air-command/horizon/03_Booster/A1_Pressure_Chamber/A2_Bottom_EndCap/P7_CF_Sleeve/info.txt

290mm long 2.5" Medium Carbon fiber sleeve
