air-command/horizon/03_Booster/A1_Pressure_Chamber/A2_Bottom_EndCap/P8_FG_Nozzle_Tow/info.txt

Nozzle is prepped by sanding and washing in Acetone. 
The nozzle is placed by itself on the nozzle mold, and 7 x 1m FG tow (made from 200gsm cloth) is wrapped around the top of the nozzle. 
This is then sanded smooth on the outside.
