air-command/horizon/03_Booster/A1_Pressure_Chamber/A3_Inner_Tube/P1_Mandrel/info.txt

80mm Diameter PVC mandrel 2m long.
Sanded smooth with 400grit and 1200grit sandpaper.
Waxed 3x with Carnauba Wax mold release.
