air-command/horizon/03_Booster/A1_Pressure_Chamber/A4_Nozzle_Oversleeve/P1_Nozzle/info.txt

The nozzle is made from a 42mm aluminium bar cut to a length of 51mm before being machined.
