air-command/horizon/03_Booster/A1_Pressure_Chamber/A4_Nozzle_Oversleeve/P2_Oring/info.txt

The oring is inserted into the nozzle sleeve to help seal.
It is a 024 o-ring.
