air-command/horizon/01_Launcher/A1_Air_Control_Box/Control_Box_Seals.JPG

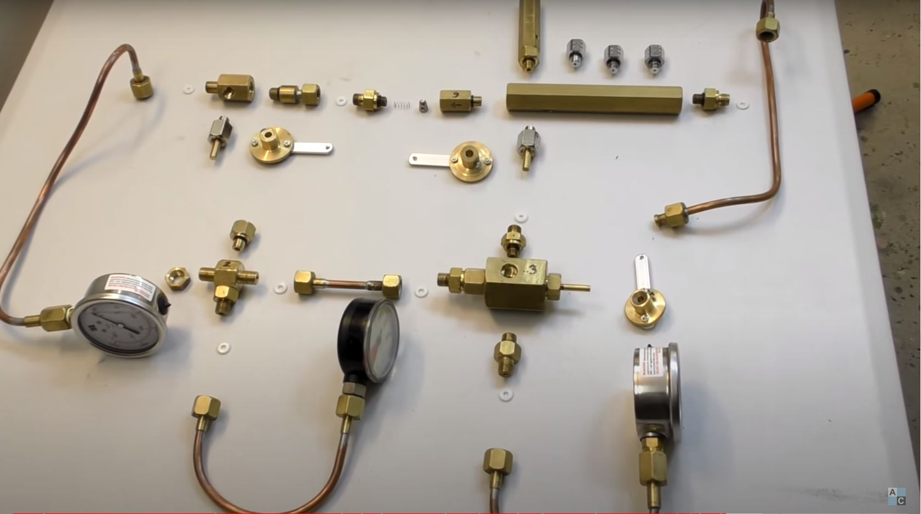
01_Launcher/A1_Air_Control_Box/Control_Box_Seals.JPG
