air-command/horizon/01_Launcher/A1_Air_Control_Box/Seals.jpg

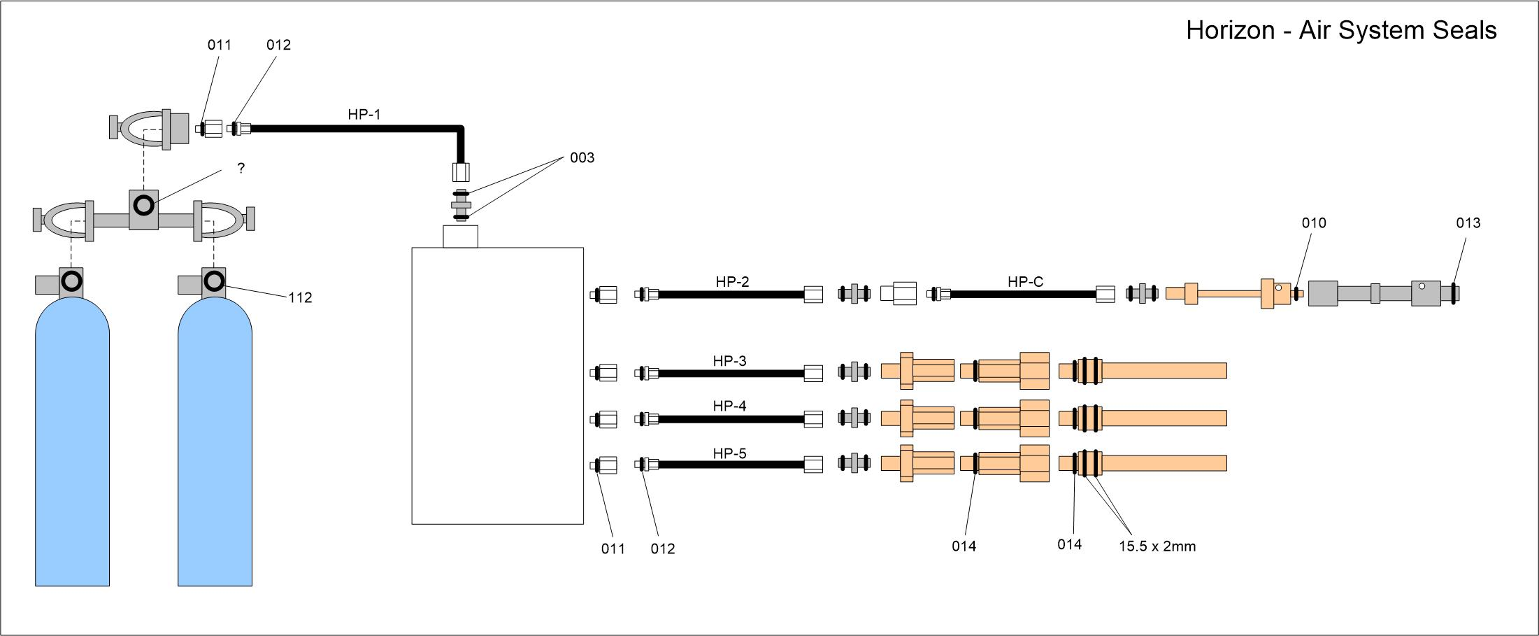
01_Launcher/A1_Air_Control_Box/Seals.jpg
