air-command/horizon/03_Booster/A2_Deployment/A2_Main_Deploy/photos/CameraPod2.jpg

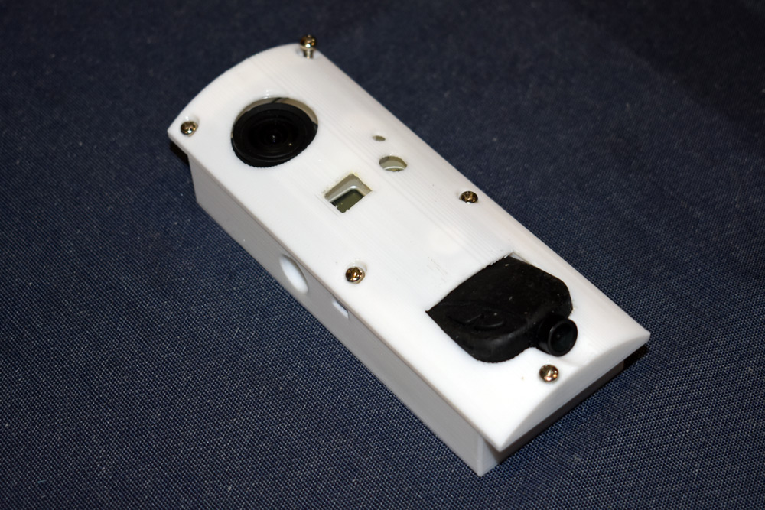
03_Booster/A2_Deployment/A2_Main_Deploy/photos/CameraPod2.jpg
