air-command/horizon/03_Booster/A2_Deployment/A2_Main_Deploy/photos/CameraPod3.jpg

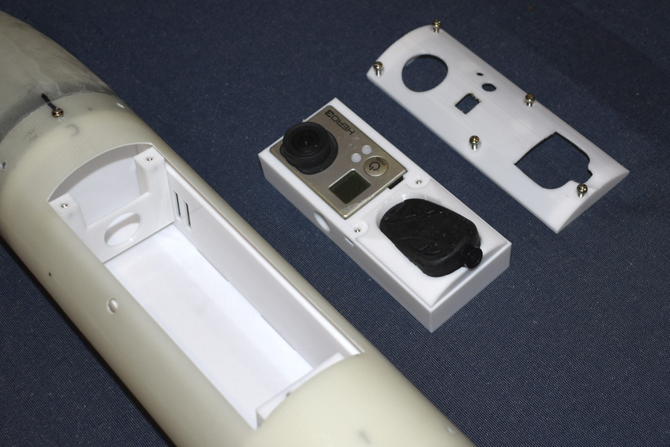
03_Booster/A2_Deployment/A2_Main_Deploy/photos/CameraPod3.jpg
