air-command/horizon/03_Booster/A3_Lower_Bracket/A3_Lower_Bracket.JPG

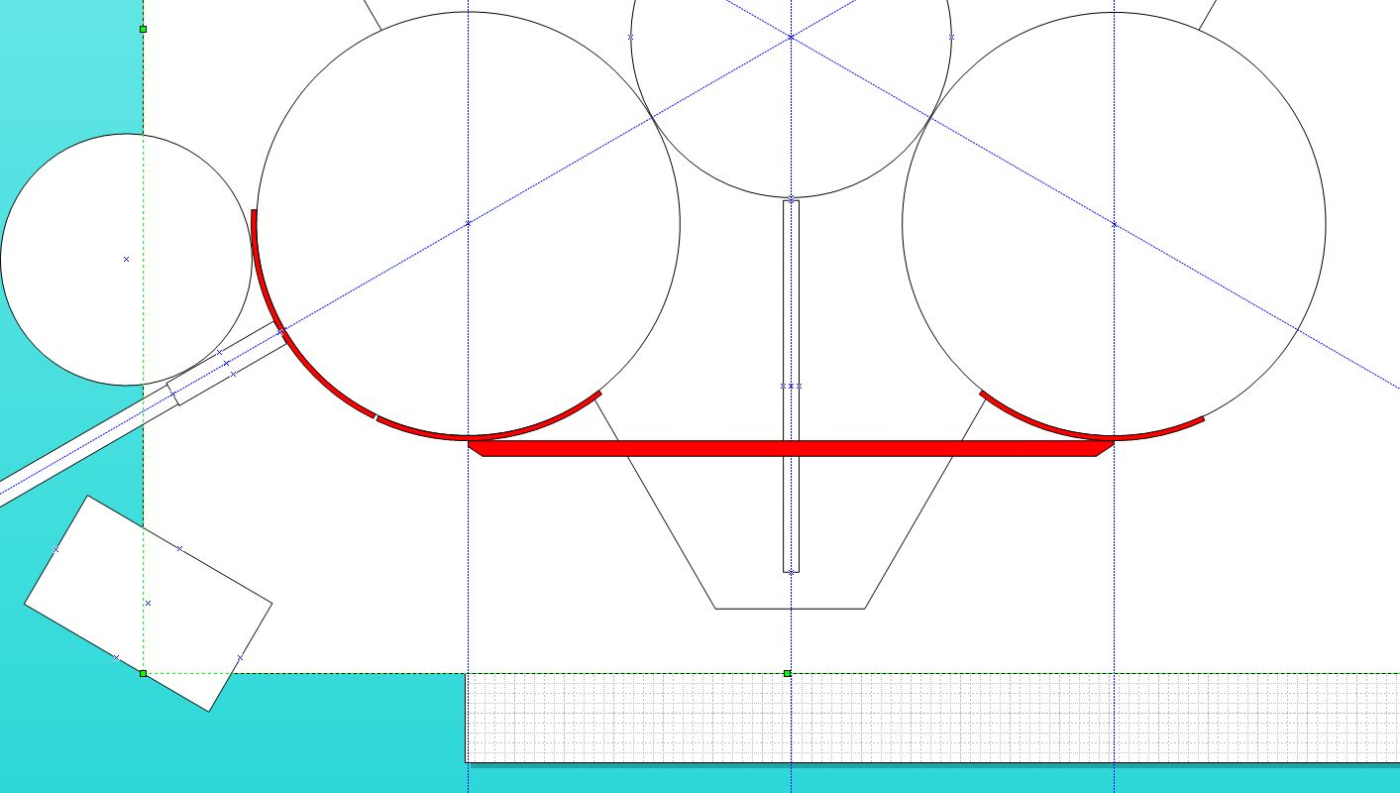
03_Booster/A3_Lower_Bracket/A3_Lower_Bracket.JPG
