air-command/horizon/03_Booster/A8_Top_Ring/ring1.jpg

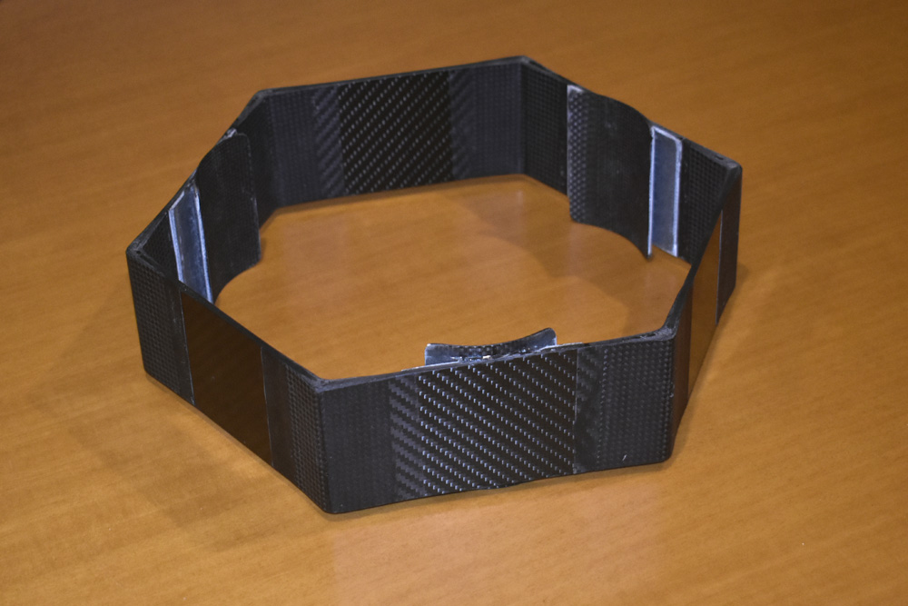
03_Booster/A8_Top_Ring/ring1.jpg
