air-command/horizon/03_Booster/A8_Top_Ring/ring2.jpg

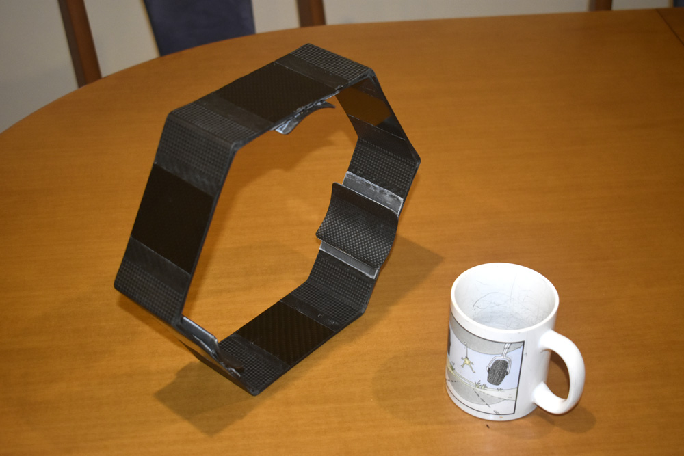
03_Booster/A8_Top_Ring/ring2.jpg
