air-command/horizon/03_Booster/A8_Top_Ring/ring3.jpg

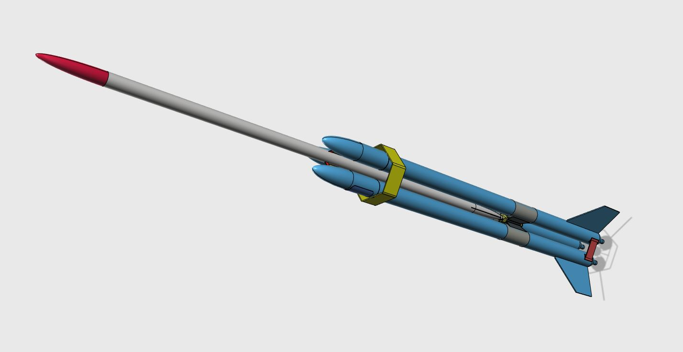
03_Booster/A8_Top_Ring/ring3.jpg
