air-command/horizon/Flight_Data/Booster/pod_a_horizon_2.JPG

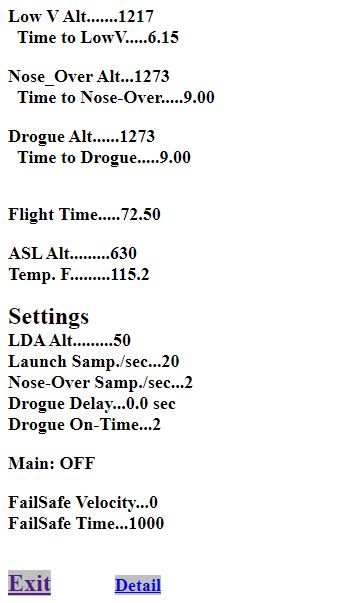
Flight_Data/Booster/pod_a_horizon_2.JPG
