air-command/horizon/Flight_Data/Booster/pod_b_horizon_1.JPG

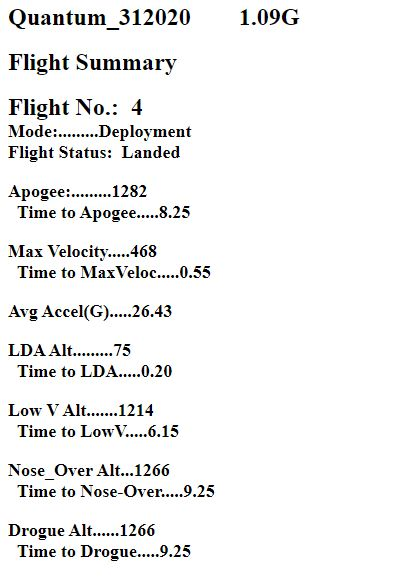
Flight_Data/Booster/pod_b_horizon_1.JPG
