air-command/horizon/Flight_Data/Sustainer/horizon.JPG

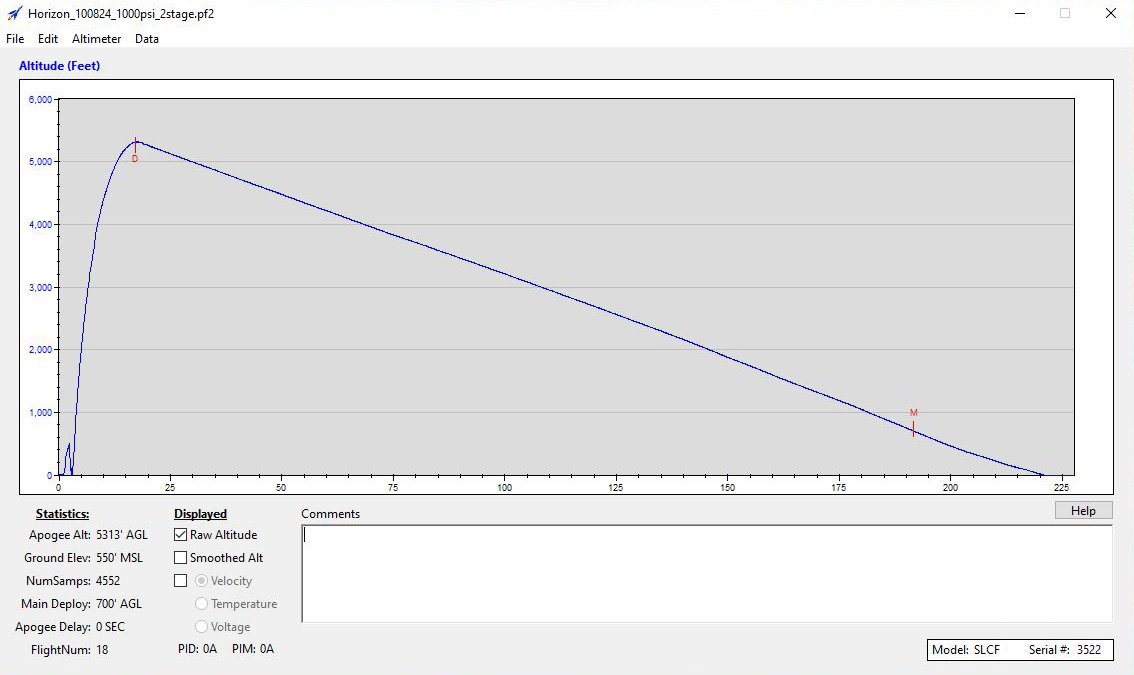
Flight_Data/Sustainer/horizon.JPG
