air-command/horizon/03_Booster/A2_Deployment/A2_Main_Deploy/P3_Body/P3_Body.stl

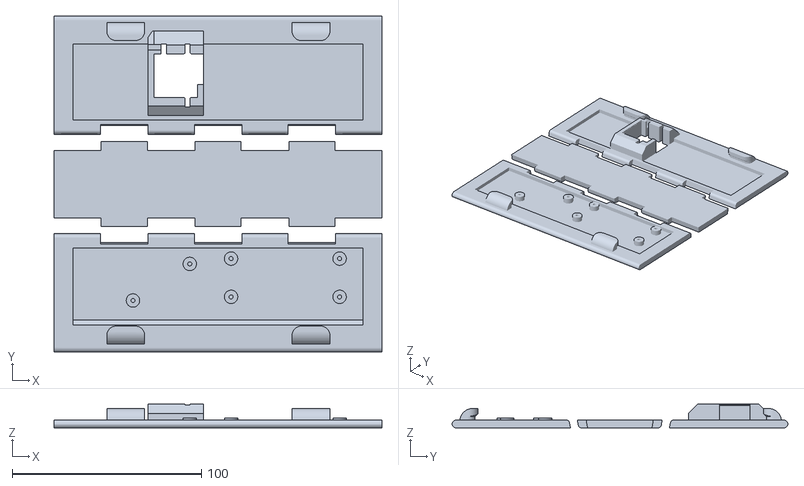
[picture p35: CAD file, 2025-02-12]
03_Booster/A2_Deployment/A2_Main_Deploy/P3_Body/P3_Body.stl
173.0 x 177.4 x 12.7
