air-command/horizon/03_Booster/A2_Deployment/A2_Main_Deploy/P3_Body_Back/P3_Body_Back.stl

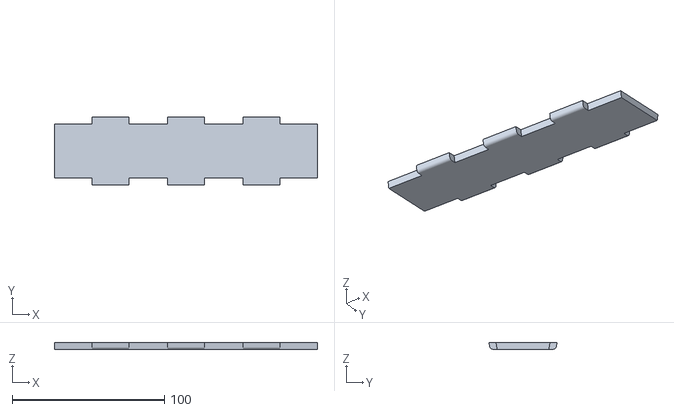
[picture p36: CAD file, 2025-02-12]
03_Booster/A2_Deployment/A2_Main_Deploy/P3_Body_Back/P3_Body_Back.stl
173.0 x 44.8 x 4.30
