air-command/horizon/03_Booster/A2_Deployment/A2_Main_Deploy/P4_Body_Servo/P4_Body_Servo.stl

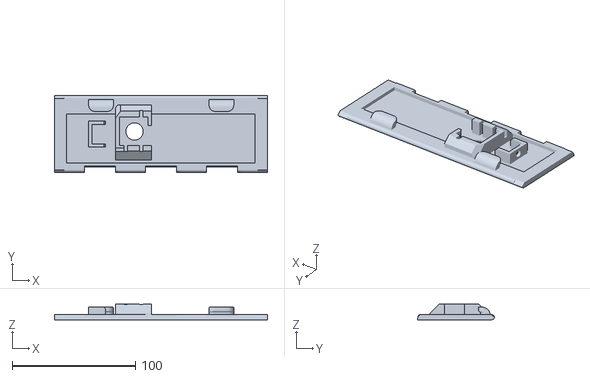
[picture p37: CAD file, 2025-02-12]
03_Booster/A2_Deployment/A2_Main_Deploy/P4_Body_Servo/P4_Body_Servo.stl
173.0 x 62.6 x 12.7
