air-command/horizon/03_Booster/A2_Deployment/A2_Main_Deploy/P5_Body_Quantum/P5_Body_Quantum.stl

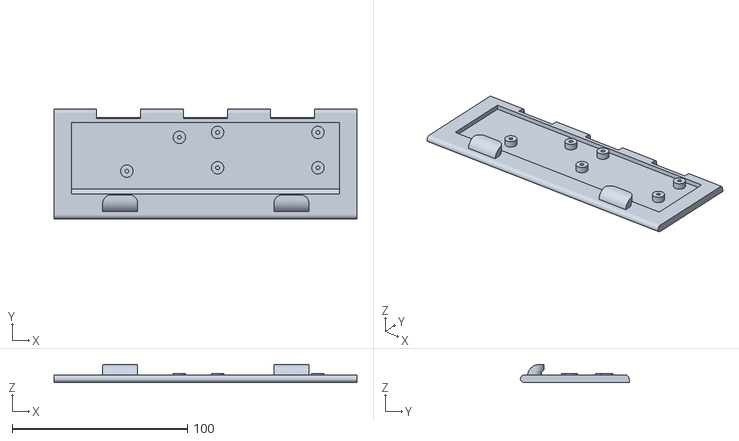
[picture p38: CAD file, 2025-02-12]
03_Booster/A2_Deployment/A2_Main_Deploy/P5_Body_Quantum/P5_Body_Quantum.stl
173.0 x 62.5 x 10.3
