air-command/horizon/03_Booster/A2_Deployment/A2_Main_Deploy/P6_Body_Rokit/P6_Body_Rokit.stl

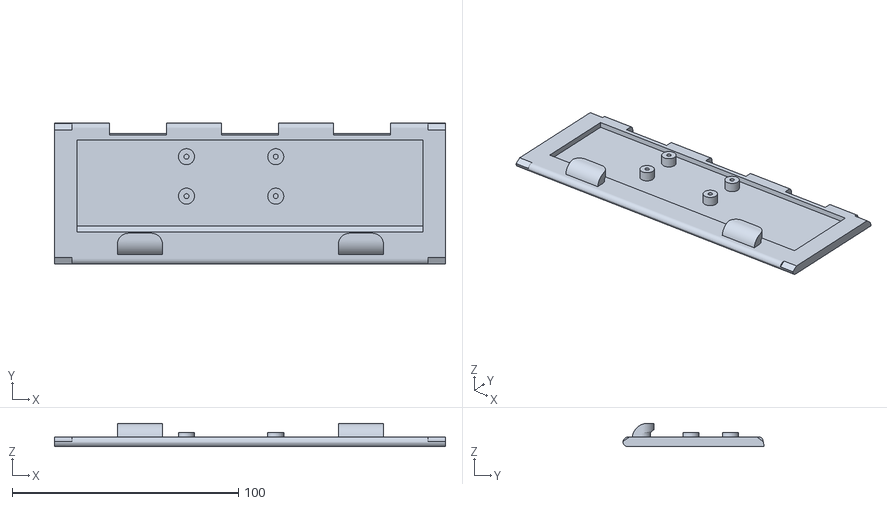
[picture p39: CAD file, 2025-02-12]
03_Booster/A2_Deployment/A2_Main_Deploy/P6_Body_Rokit/P6_Body_Rokit.stl
173.0 x 62.5 x 10.3
