air-command/horizon/03_Booster/A2_Deployment/A2_Main_Deploy/P7_Battery_Holder_A/P7_Battery_Holder_A.stl

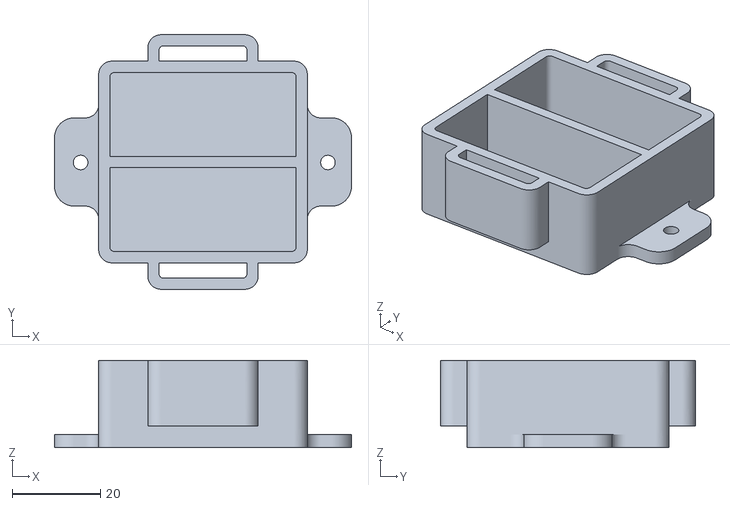
[picture p40: CAD file, 2025-02-12]
03_Booster/A2_Deployment/A2_Main_Deploy/P7_Battery_Holder_A/P7_Battery_Holder_A.stl
67.3 x 57.6 x 19.8
