air-command/horizon/03_Booster/A2_Deployment/A2_Main_Deploy/P8_Battery_Holder_B/P8_Battery_Holder_B.stl

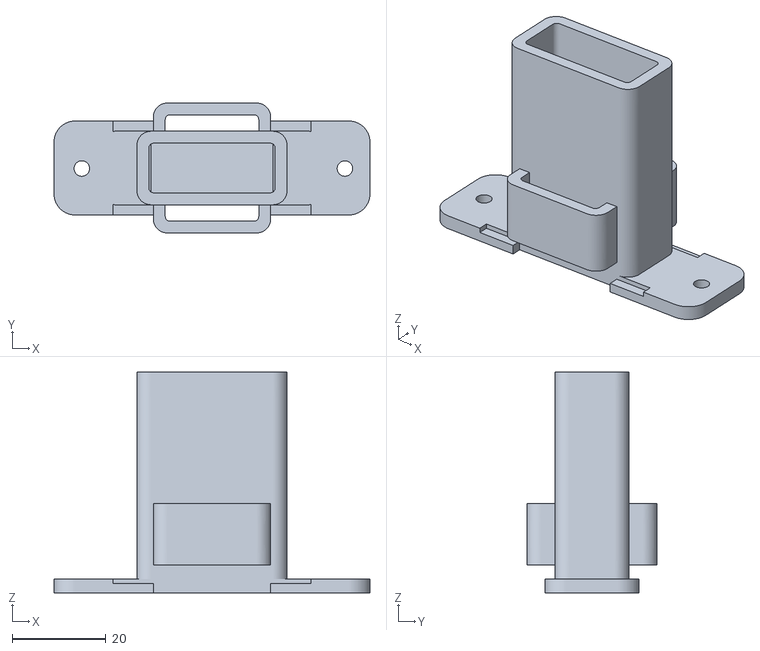
[picture p41: CAD file, 2025-02-12]
03_Booster/A2_Deployment/A2_Main_Deploy/P8_Battery_Holder_B/P8_Battery_Holder_B.stl
67.3 x 27.6 x 47.0
