air-command/horizon/03_Booster/A2_Deployment/A2_Main_Deploy/P9_Ejector_Plate/P9_Ejector_Plate.stl

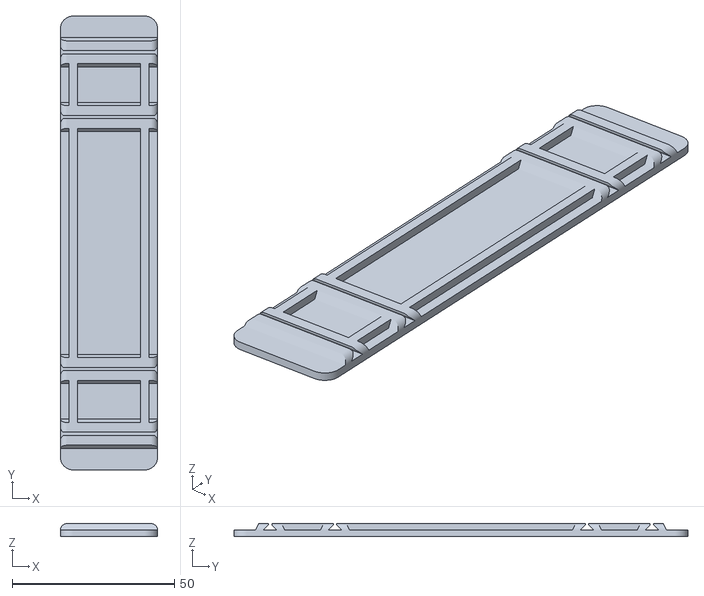
[picture p42: CAD file, 2025-02-12]
03_Booster/A2_Deployment/A2_Main_Deploy/P9_Ejector_Plate/P9_Ejector_Plate.stl
30.0 x 140.0 x 4.00
