air-command/horizon/03_Booster/A2_Deployment/A3_Camera_Pod/A1_Cameras/P4_Camera_Mounts.stl

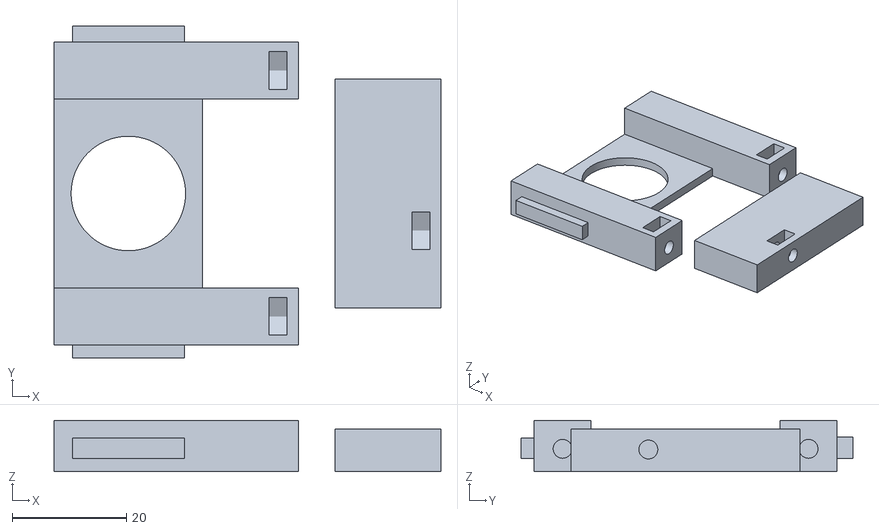
[picture p43: CAD file, 2025-02-12]
03_Booster/A2_Deployment/A3_Camera_Pod/A1_Cameras/P4_Camera_Mounts.stl
67.7 x 58.0 x 9.00
