air-command/horizon/03_Booster/A2_Deployment/A3_Camera_Pod/GOPRO_HERO_3.stp

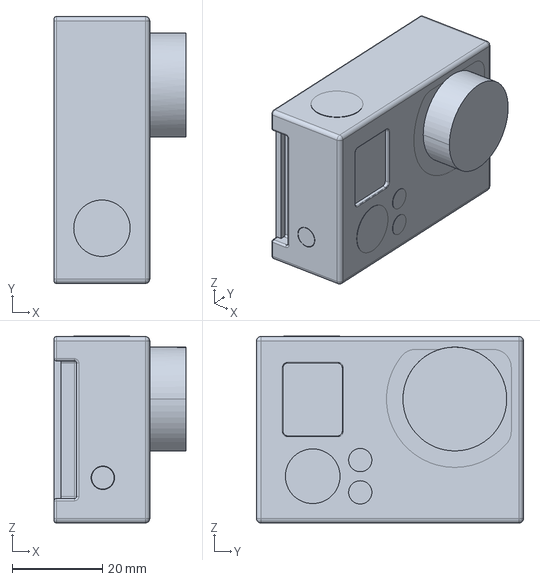
[picture p44: CAD file, 2025-02-12]
03_Booster/A2_Deployment/A3_Camera_Pod/GOPRO_HERO_3.stp
29.2 x 59.1 x 41.4 mm
