air-command/horizon/03_Booster/A2_Deployment/A3_Camera_Pod/P1_Top_Bulkhead/P1_Top_Bulkhead.stl

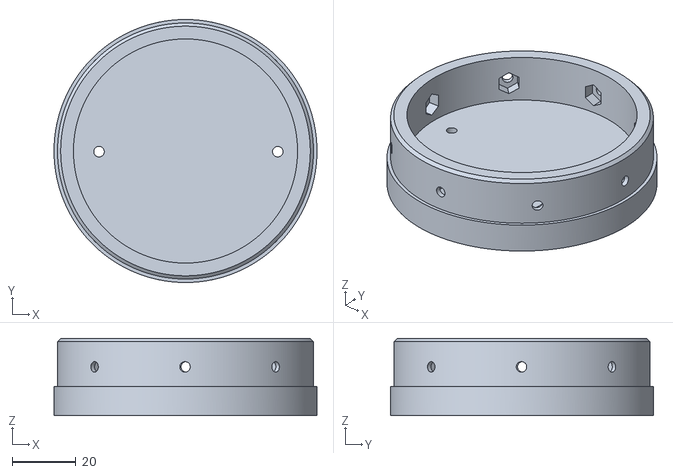
[picture p45: CAD file, 2025-02-12]
03_Booster/A2_Deployment/A3_Camera_Pod/P1_Top_Bulkhead/P1_Top_Bulkhead.stl
82.4 x 82.4 x 24.2
