air-command/horizon/03_Booster/A2_Deployment/A3_Camera_Pod/P2_Bottom_Bulkhead/P2_Bottom_Bulkhead.stl

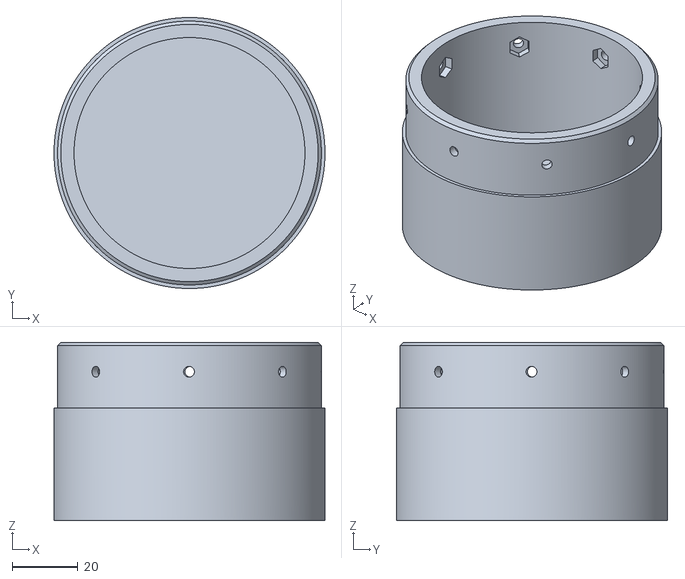
[picture p46: CAD file, 2025-02-12]
03_Booster/A2_Deployment/A3_Camera_Pod/P2_Bottom_Bulkhead/P2_Bottom_Bulkhead.stl
82.4 x 82.4 x 54.2
