air-command/horizon/03_Booster/A2_Deployment/A3_Camera_Pod/P3_Body_Back/P3_Body_Back.stl

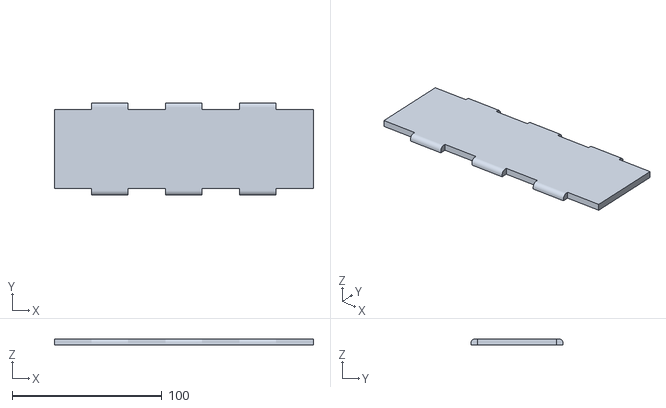
[picture p47: CAD file, 2025-02-12]
03_Booster/A2_Deployment/A3_Camera_Pod/P3_Body_Back/P3_Body_Back.stl
173.0 x 61.5 x 4.30
