air-command/horizon/03_Booster/A2_Deployment/A3_Camera_Pod/P4_Body_Left/P4_Body_Left.stl

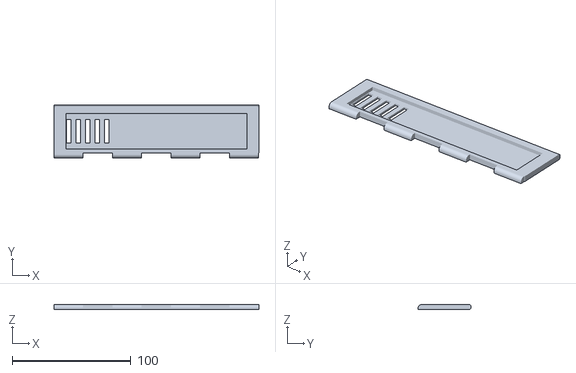
[picture p48: CAD file, 2025-02-12]
03_Booster/A2_Deployment/A3_Camera_Pod/P4_Body_Left/P4_Body_Left.stl
173.0 x 44.5 x 4.30
