air-command/horizon/03_Booster/A2_Deployment/A3_Camera_Pod/P6_Battery_808/P6_Battery_808.stl

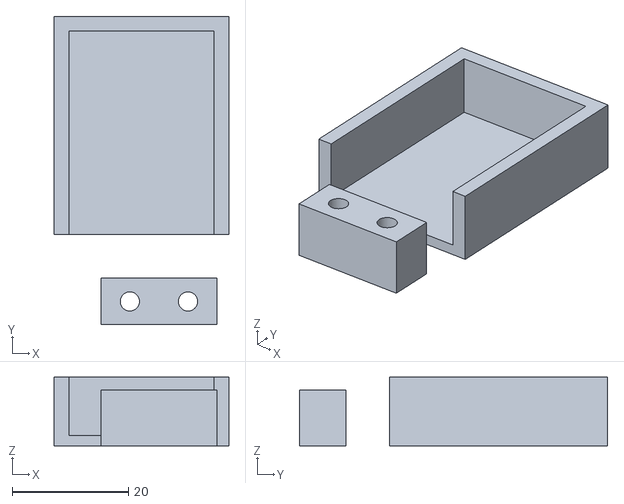
[picture p49: CAD file, 2025-02-12]
03_Booster/A2_Deployment/A3_Camera_Pod/P6_Battery_808/P6_Battery_808.stl
30.1 x 53.1 x 11.8
