air-command/horizon/03_Booster/A4_Coupler/P1_Coupler_Mold/P1_Coupler_Mold.stl

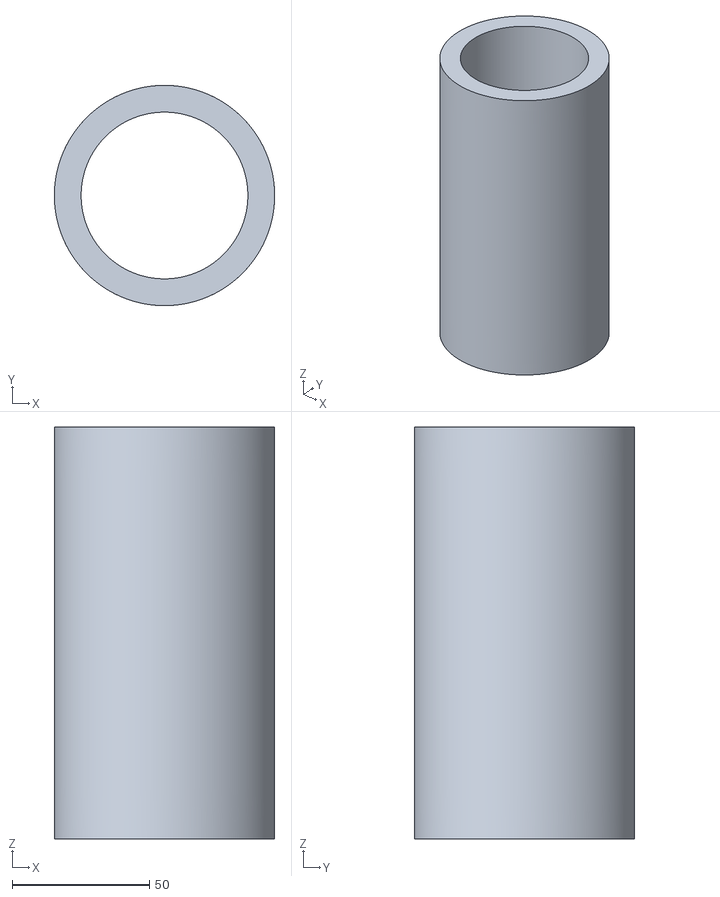
[picture p50: CAD file, 2025-02-12]
03_Booster/A4_Coupler/P1_Coupler_Mold/P1_Coupler_Mold.stl
80.2 x 80.2 x 150.0
