air-command/horizon/03_Booster/A7_Middle_Bracket/A1_Stager/P1_Servo_Mount/servomount_8_parts.stl

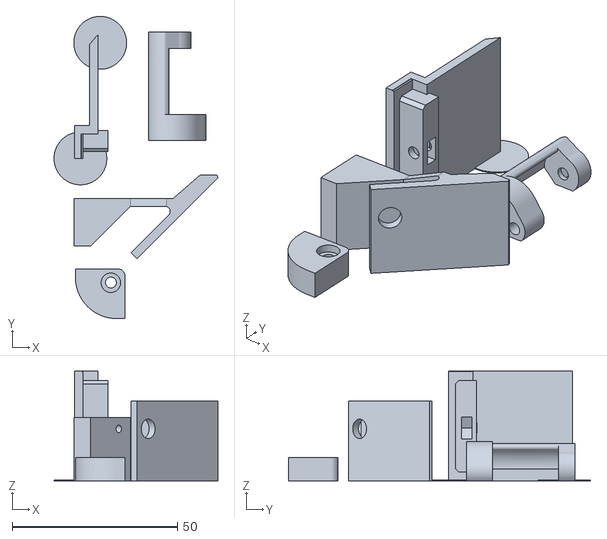
[picture p51: CAD file, 2025-02-12]
03_Booster/A7_Middle_Bracket/A1_Stager/P1_Servo_Mount/servomount_8_parts.stl
49.7 x 91.5 x 33.2
