air-command/horizon/03_Booster/A7_Middle_Bracket/P1_Segment_Spacer/P1_Segment_Spacer.stl

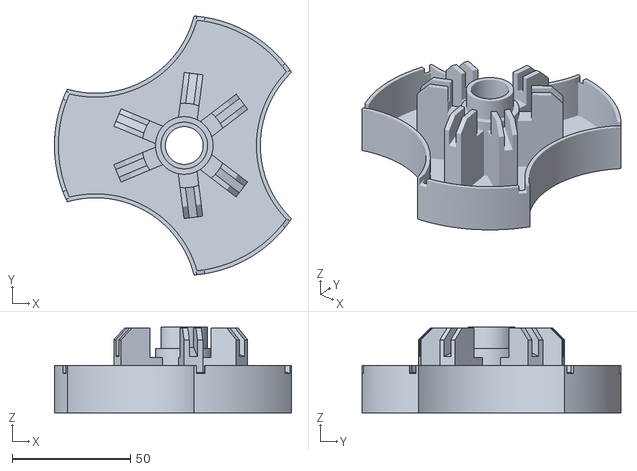
[picture p53: CAD file, 2025-02-12]
03_Booster/A7_Middle_Bracket/P1_Segment_Spacer/P1_Segment_Spacer.stl
100.4 x 109.7 x 36.4
