air-command/horizon/03_Booster/A7_Middle_Bracket/P5_Wedge_Narrow/P5_Wedge_mold.stl

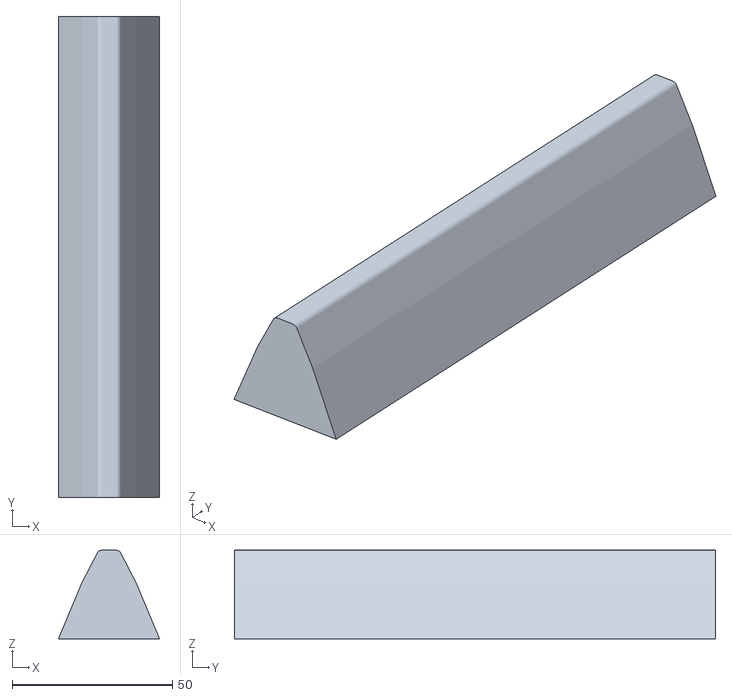
[picture p54: CAD file, 2025-02-12]
03_Booster/A7_Middle_Bracket/P5_Wedge_Narrow/P5_Wedge_mold.stl
31.5 x 150.0 x 27.6
