air-command/horizon/03_Booster/A7_Middle_Bracket/P7_Wedge_Wide/P7_Wedge_Wide.stl

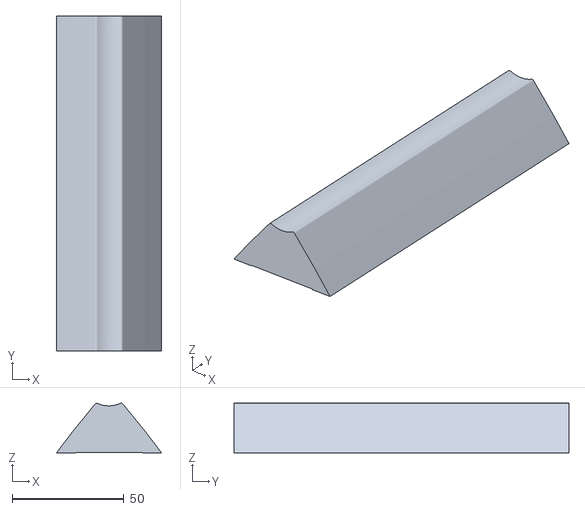
[picture p55: CAD file, 2025-02-12]
03_Booster/A7_Middle_Bracket/P7_Wedge_Wide/P7_Wedge_Wide.stl
47.1 x 150.0 x 22.3
