air-command/horizon/03_Booster/A7_Middle_Bracket/P8_Wedge_Pad/P8_Wedge_Pad.stl

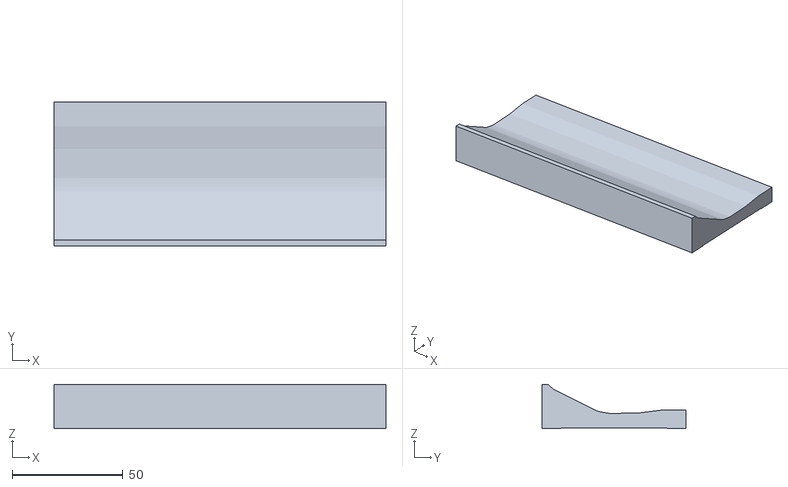
[picture p56: CAD file, 2025-02-12]
03_Booster/A7_Middle_Bracket/P8_Wedge_Pad/P8_Wedge_Pad.stl
150.0 x 65.0 x 20.0
