air-command/horizon/03_Booster/A8_Top_Ring/P1_Wedges/P1_Wedges.stl

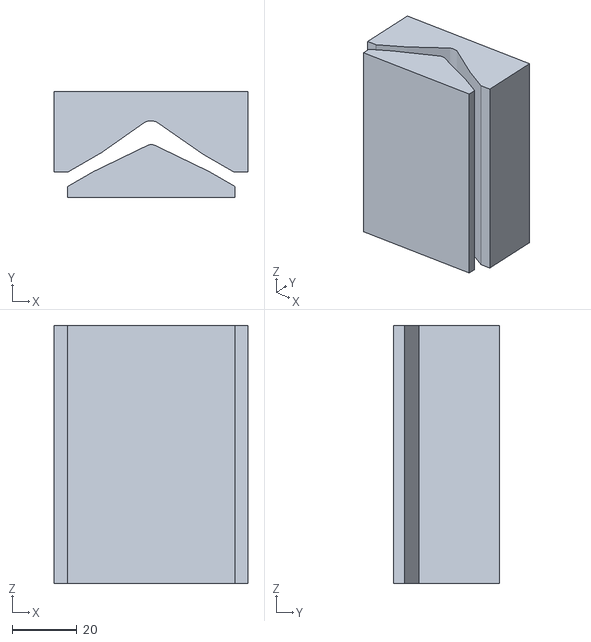
[picture p57: CAD file, 2025-02-12]
03_Booster/A8_Top_Ring/P1_Wedges/P1_Wedges.stl
60.0 x 32.9 x 80.0
