air-command/horizon/03_Booster/A9_Fins/P1_Fin Fillets/P1_Fin_Fillets.stl

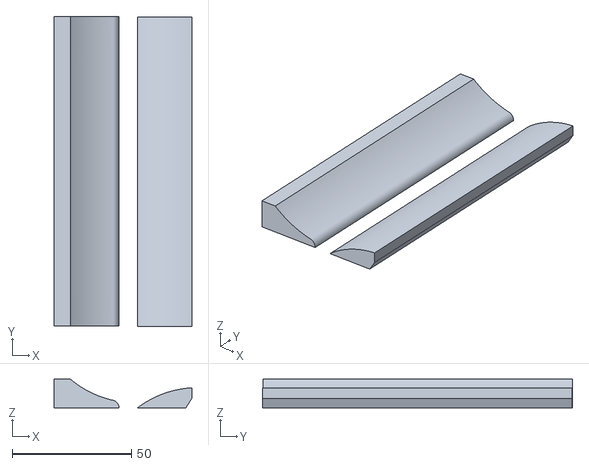
[picture p58: CAD file, 2025-02-12]
03_Booster/A9_Fins/P1_Fin Fillets/P1_Fin_Fillets.stl
57.8 x 130.1 x 12.1
