air-command/horizon/03_Booster/A1_Pressure_Chamber/A2_Bottom_EndCap/P4_Nozzle_Extension/P4_Nozzle_Extension.stl

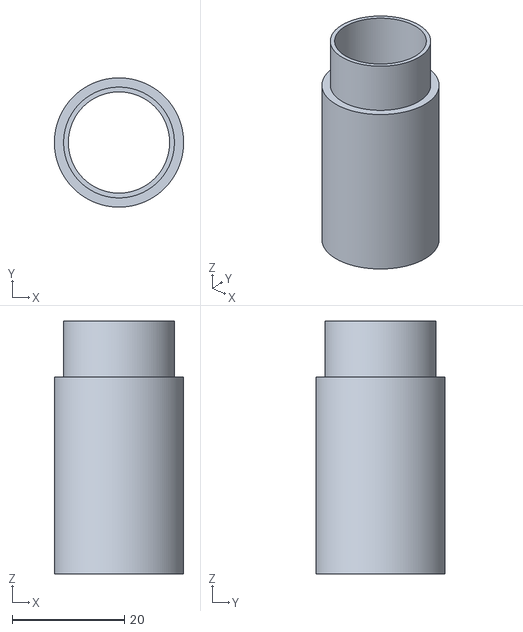
[picture p59: CAD file, 2025-02-12]
03_Booster/A1_Pressure_Chamber/A2_Bottom_EndCap/P4_Nozzle_Extension/P4_Nozzle_Extension.stl
23.0 x 23.0 x 45.0
