air-command/horizon/03_Booster/A2_Deployment/A2_Main_Deploy/P3_Body/P3_Body_servo.stl

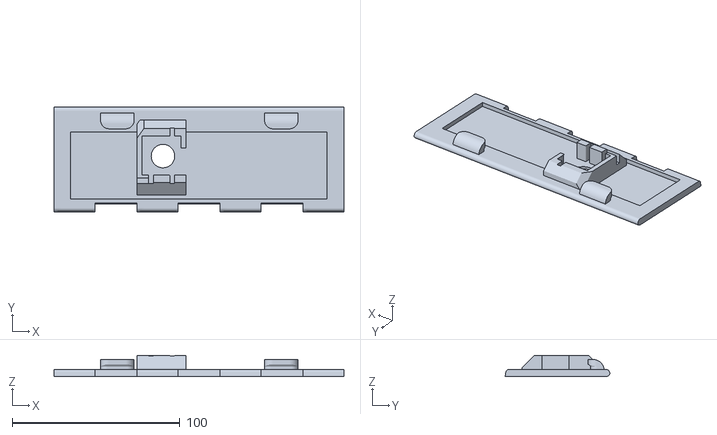
[picture p60: CAD file, 2025-02-12]
03_Booster/A2_Deployment/A2_Main_Deploy/P3_Body/P3_Body_servo.stl
173.0 x 62.6 x 12.7
