air-command/horizon/03_Booster/A2_Deployment/A2_Main_Deploy/P4_Body_Servo/switch_holder.stl

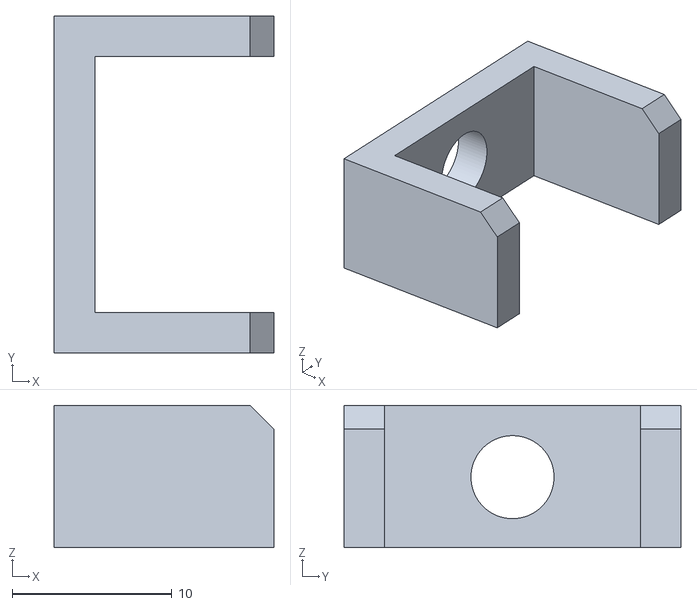
[picture p61: CAD file, 2025-02-12]
03_Booster/A2_Deployment/A2_Main_Deploy/P4_Body_Servo/switch_holder.stl
13.8 x 21.1 x 8.92
