air-command/horizon/03_Booster/A2_Deployment/A3_Camera_Pod/A1_Cameras/p1.stl

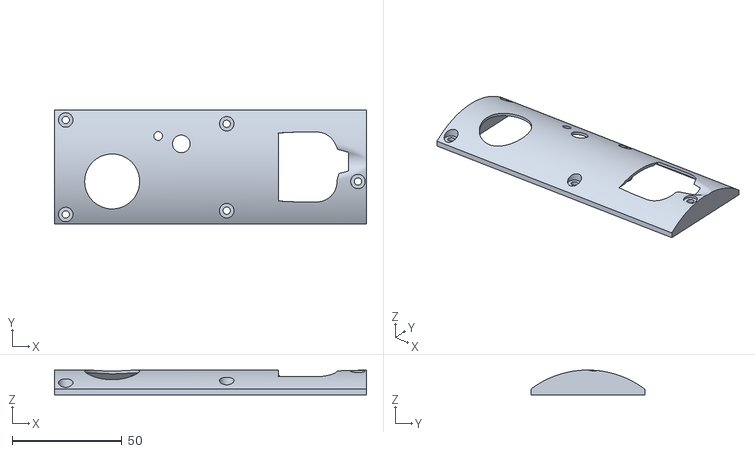
[picture p62: CAD file, 2025-02-12]
03_Booster/A2_Deployment/A3_Camera_Pod/A1_Cameras/p1.stl
142.0 x 52.0 x 11.3
