air-command/horizon/03_Booster/A2_Deployment/A3_Camera_Pod/GoPro_Hero_3_Frame.A.7.stp

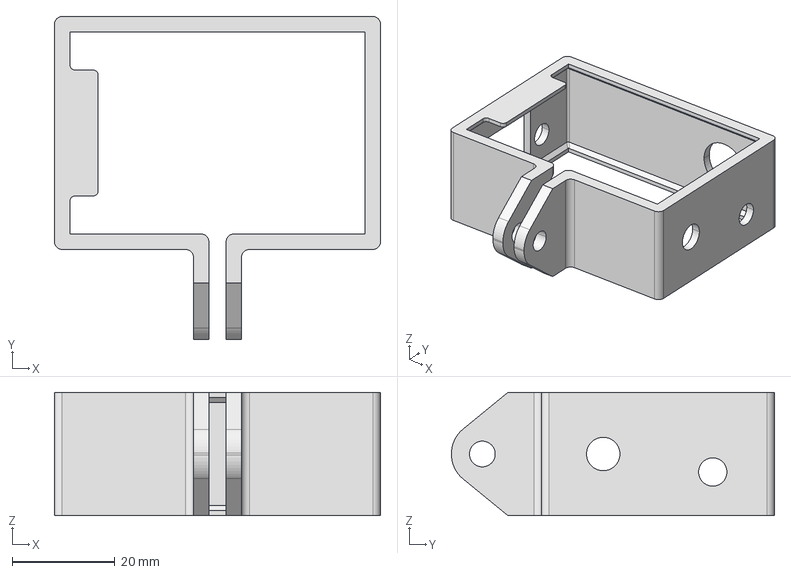
[picture p63: CAD file, 2025-02-12]
03_Booster/A2_Deployment/A3_Camera_Pod/GoPro_Hero_3_Frame.A.7.stp
63.4 x 62.8 x 24.0 mm
