air-command/horizon/03_Booster/A7_Middle_Bracket/A1_Stager/P1_Servo_Mount/servomount_6.stl

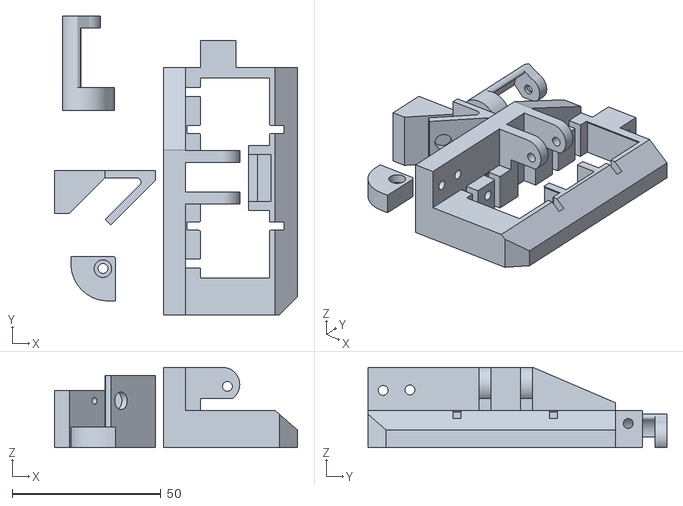
[picture p64: CAD file, 2025-02-12]
03_Booster/A7_Middle_Bracket/A1_Stager/P1_Servo_Mount/servomount_6.stl
81.8 x 100.6 x 27.0
