air-command/horizon/03_Booster/A7_Middle_Bracket/A2_Battery_Holder/P1_Battery_Holder/P1_Battery_Holder.stl

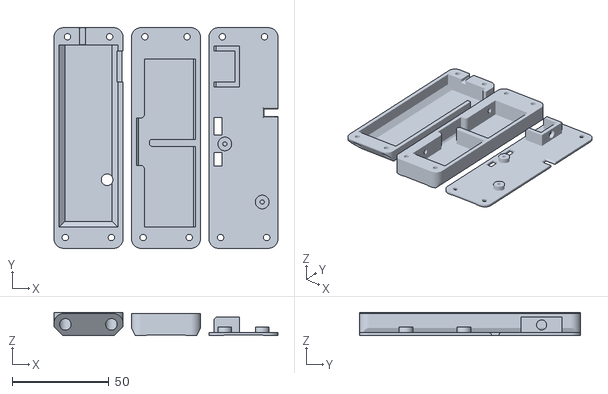
[picture p65: CAD file, 2025-02-12]
03_Booster/A7_Middle_Bracket/A2_Battery_Holder/P1_Battery_Holder/P1_Battery_Holder.stl
115.7 x 114.0 x 12.0
