air-command/horizon/03_Booster/A2_Deployment/A3_Camera_Pod/A1_Cameras/P3_Camera_Body.stl

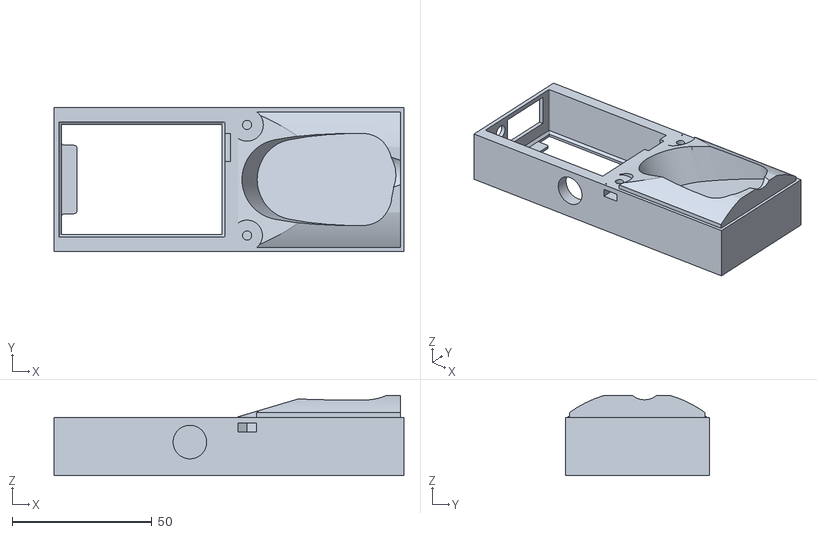
[picture p66: CAD file, 2025-02-12]
03_Booster/A2_Deployment/A3_Camera_Pod/A1_Cameras/P3_Camera_Body.stl
125.2 x 51.5 x 28.7
