air-command/horizon/03_Booster/A7_Middle_Bracket/A1_Stager/P1_Servo_Mount/servomount_7_parts.stl

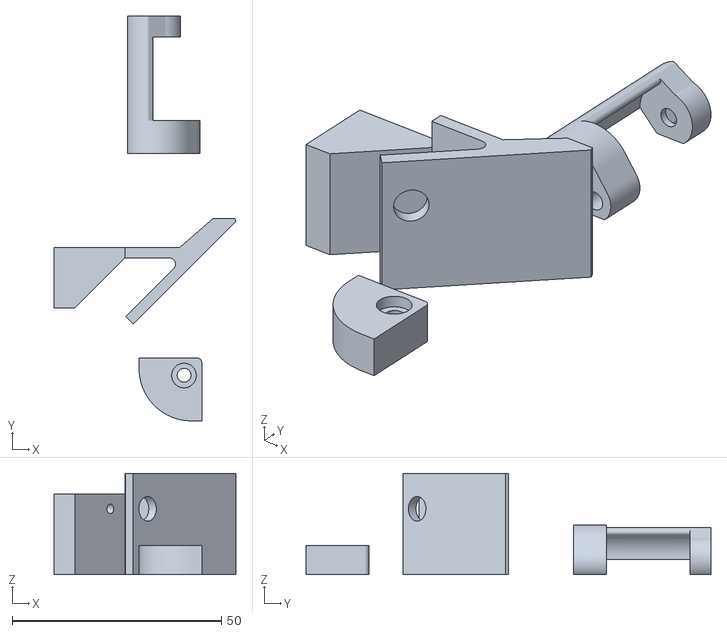
[picture p67: CAD file, 2025-02-12]
03_Booster/A7_Middle_Bracket/A1_Stager/P1_Servo_Mount/servomount_7_parts.stl
43.5 x 96.8 x 24.2
