air-command/horizon/03_Booster/A7_Middle_Bracket/A1_Stager/P1_Servo_Mount/servomount_4.stl

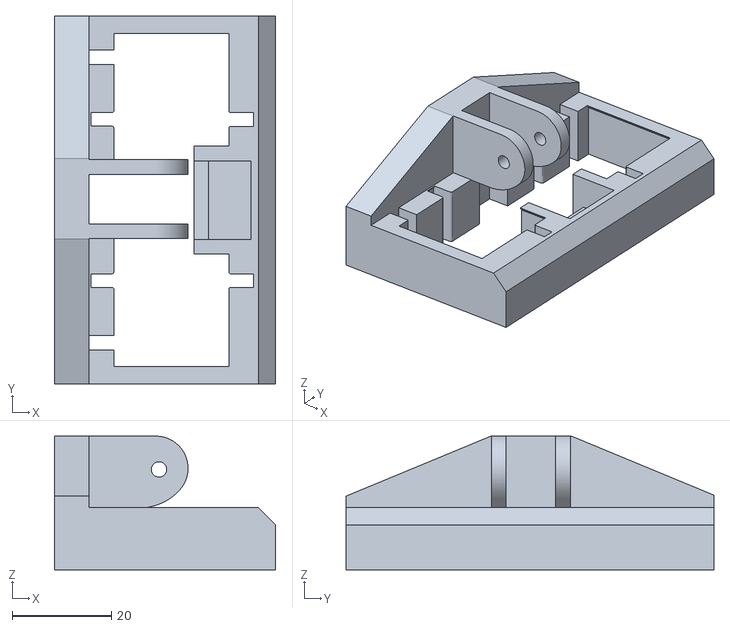
[picture p68: CAD file, 2025-02-12]
03_Booster/A7_Middle_Bracket/A1_Stager/P1_Servo_Mount/servomount_4.stl
44.7 x 74.3 x 27.0
