air-command/horizon/03_Booster/A7_Middle_Bracket/A1_Stager/P1_Servo_Mount/servomount_5.stl

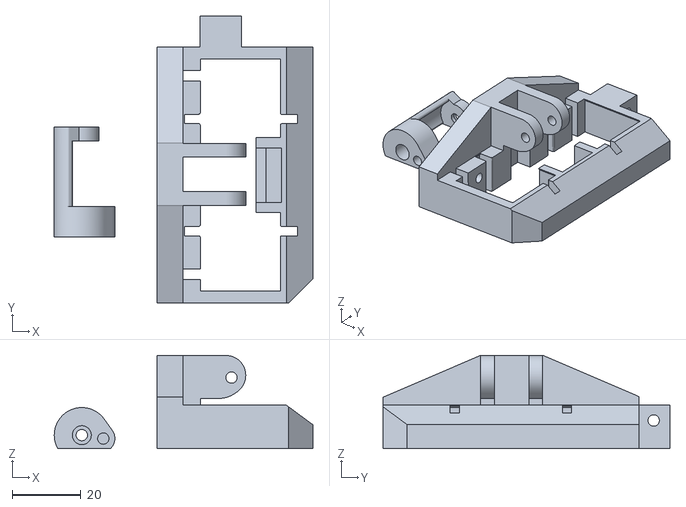
[picture p69: CAD file, 2025-02-12]
03_Booster/A7_Middle_Bracket/A1_Stager/P1_Servo_Mount/servomount_5.stl
75.0 x 83.3 x 27.0
