air-command/horizon/01_Launcher/A5_Controller/Launcher_Wiring_V4.png

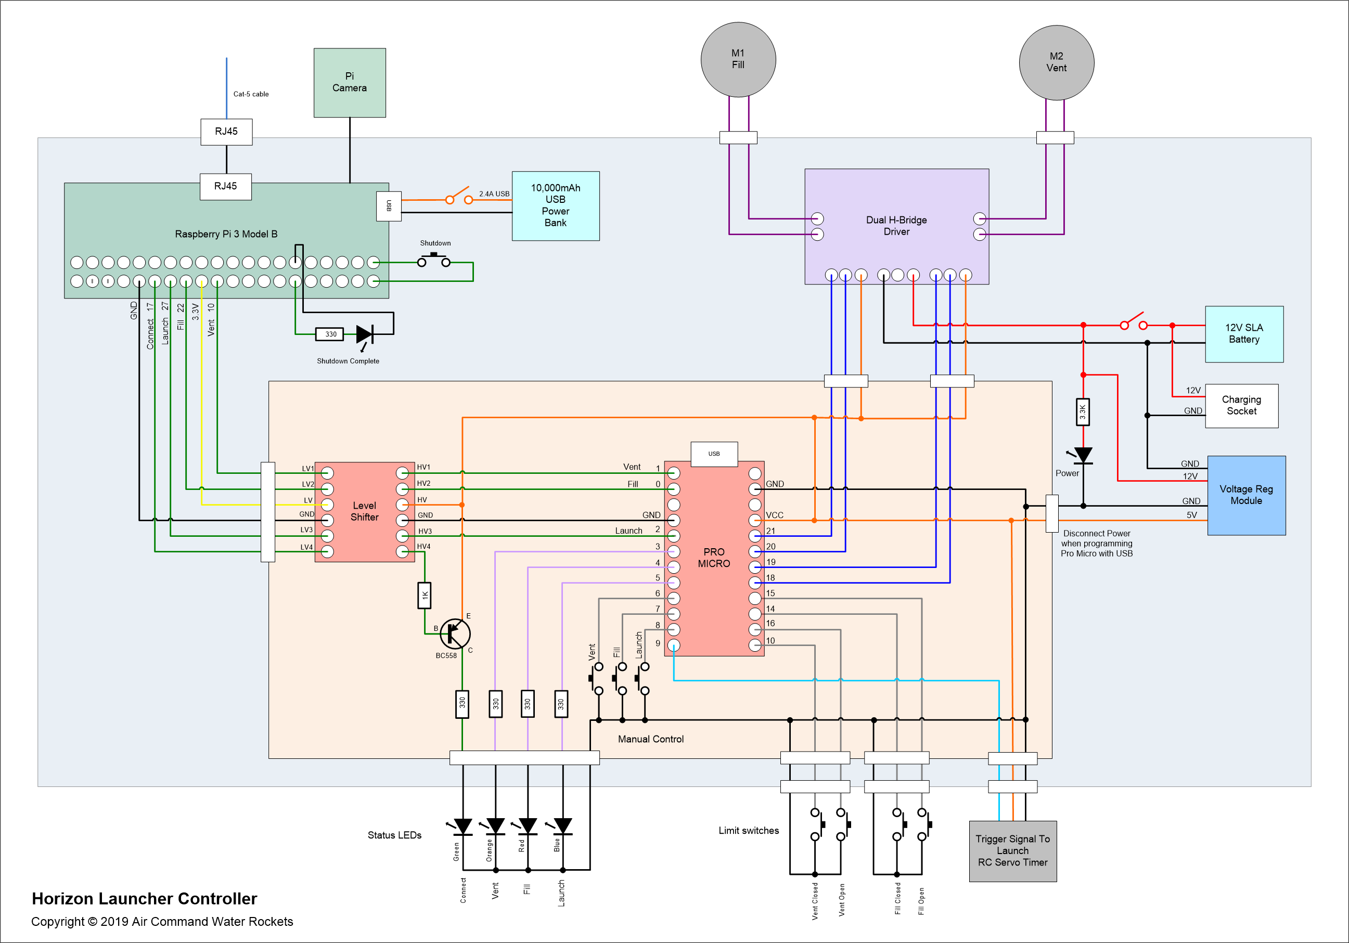
01_Launcher/A5_Controller/Launcher_Wiring_V4.png
